AhmedHassanien34/Smart-Home/1- Code/Smart_Home_Master/MCAL/DIO/DIO_program.c

/**************************************************************************************/
/********************			Author: Ahmed Mohamed			***********************/
/********************			Layer: MCAL			 			***********************/
/********************			Component: DIO 				    ***********************/
/********************			Version: 2.00		 			***********************/
/********************			Date: 29-1-2023	 				***********************/
/**************************************************************************************/


#include "STD_TYPES.h"
#include "BIT_MATH.h"

#include "DIO_interface.h"
#include "DIO_register.h"
#include "DIO_private.h"
#include "DIO_config.h"


void DIO_voidInit(void)
{
	DIO_u8SetPinDirection(DIO_u8PORTA,DIO_u8PIN0,DIO_u8PIN_INPUT);
	DIO_u8SetPinDirection(DIO_u8PORTA,DIO_u8PIN1,DIO_u8PIN_INPUT);
	DIO_u8SetPinDirection(DIO_u8PORTA,DIO_u8PIN2,DIO_u8PIN_INPUT);
	DIO_u8SetPinDirection(DIO_u8PORTA,DIO_u8PIN3,DIO_u8PIN_INPUT);
	DIO_u8SetPinDirection(DIO_u8PORTA,DIO_u8PIN4,DIO_u8PIN_INPUT);
	DIO_u8SetPinDirection(DIO_u8PORTA,DIO_u8PIN5,DIO_u8PIN_INPUT);
	DIO_u8SetPinDirection(DIO_u8PORTA,DIO_u8PIN6,DIO_u8PIN_INPUT);

	DIO_u8SetPinDirection(DIO_u8PORTB,DIO_u8PIN0,DIO_u8PIN_OUTPUT);
	DIO_u8SetPinDirection(DIO_u8PORTB,DIO_u8PIN1,DIO_u8PIN_OUTPUT);

	DIO_u8SetPinDirection(DIO_u8PORTC,DIO_u8PIN0,DIO_u8PIN_OUTPUT);
	DIO_u8SetPinDirection(DIO_u8PORTC,DIO_u8PIN1,DIO_u8PIN_OUTPUT);
	DIO_u8SetPinDirection(DIO_u8PORTC,DIO_u8PIN2,DIO_u8PIN_OUTPUT);
	DIO_u8SetPinDirection(DIO_u8PORTC,DIO_u8PIN3,DIO_u8PIN_OUTPUT);
	DIO_u8SetPinDirection(DIO_u8PORTC,DIO_u8PIN4,DIO_u8PIN_OUTPUT);
	DIO_u8SetPinDirection(DIO_u8PORTC,DIO_u8PIN5,DIO_u8PIN_OUTPUT);
	DIO_u8SetPinDirection(DIO_u8PORTC,DIO_u8PIN6,DIO_u8PIN_OUTPUT);
	DIO_u8SetPinDirection(DIO_u8PORTC,DIO_u8PIN7,DIO_u8PIN_OUTPUT);

	DIO_u8SetPinDirection(DIO_u8PORTD,DIO_u8PIN6,DIO_u8PIN_OUTPUT);
}

u8 DIO_u8SetPinDirection(u8 Copy_u8Port, u8 Copy_u8Pin, u8 Copy_u8Direction)
{
	u8 Local_u8ErrorState=0;

	if(Copy_u8Pin <= DIO_u8PIN7)
	{
		if(Copy_u8Direction==DIO_u8PIN_INPUT)
		{
			switch(Copy_u8Port)
			{
			case DIO_u8PORTA: CLR_BIT(DDRA,Copy_u8Pin); break;
			case DIO_u8PORTB: CLR_BIT(DDRB,Copy_u8Pin); break;
			case DIO_u8PORTC: CLR_BIT(DDRC,Copy_u8Pin); break;
			case DIO_u8PORTD: CLR_BIT(DDRD,Copy_u8Pin); break;
			default: Local_u8ErrorState=1; break;
			}
		}
		else if (Copy_u8Direction==DIO_u8PIN_OUTPUT)
		{
			switch(Copy_u8Port)
			{
			case DIO_u8PORTA: SET_BIT(DDRA,Copy_u8Pin); break;
			case DIO_u8PORTB: SET_BIT(DDRB,Copy_u8Pin); break;
			case DIO_u8PORTC: SET_BIT(DDRC,Copy_u8Pin); break;
			case DIO_u8PORTD: SET_BIT(DDRD,Copy_u8Pin); break;
			default: Local_u8ErrorState=1; break;
			}
		}
		else if (Copy_u8Direction==DIO_u8PIN_INPULLUP)
		{
			switch(Copy_u8Port)
			{
			case DIO_u8PORTA: CLR_BIT(DDRA,Copy_u8Pin); SET_BIT(PORTA,Copy_u8Pin); break;
			case DIO_u8PORTB: CLR_BIT(DDRB,Copy_u8Pin); SET_BIT(PORTB,Copy_u8Pin); break;
			case DIO_u8PORTC: CLR_BIT(DDRC,Copy_u8Pin); SET_BIT(PORTC,Copy_u8Pin); break;
			case DIO_u8PORTD: CLR_BIT(DDRD,Copy_u8Pin); SET_BIT(PORTD,Copy_u8Pin); break;
			default: Local_u8ErrorState=1; break;
			}
		}
		else
		{
			Local_u8ErrorState=1;
		}
	}
	else
	{
		Local_u8ErrorState=1;
	}

	return Local_u8ErrorState;
}

u8 DIO_u8SetPortDirection(u8 Copy_u8Port, u8 Copy_u8Direction)
{
	u8 Local_u8ErrorState=0;

	switch(Copy_u8Port)
	{
	case DIO_u8PORTA : DDRA = Copy_u8Direction; break;
	case DIO_u8PORTB : DDRB = Copy_u8Direction; break;
	case DIO_u8PORTC : DDRC = Copy_u8Direction; break;
	case DIO_u8PORTD : DDRD = Copy_u8Direction; break;
	default: Local_u8ErrorState=1;
	}

	return Local_u8ErrorState;
}

u8 DIO_u8SetPinValue(u8 Copy_u8Port, u8 Copy_u8Pin, u8 Copy_u8Value)
{
	u8 Local_u8ErrorState=0;

	if(Copy_u8Pin<= DIO_u8PIN7)
	{
		if(Copy_u8Value==DIO_u8PIN_LOW)
		{
			switch(Copy_u8Port)
			{
			case DIO_u8PORTA: CLR_BIT(PORTA,Copy_u8Pin); break;
			case DIO_u8PORTB: CLR_BIT(PORTB,Copy_u8Pin); break;
			case DIO_u8PORTC: CLR_BIT(PORTC,Copy_u8Pin); break;
			case DIO_u8PORTD: CLR_BIT(PORTD,Copy_u8Pin); break;
			default: Local_u8ErrorState=1; break;
			}
		}
		else if (Copy_u8Value==DIO_u8PIN_HIGH)
		{
			switch(Copy_u8Port)
			{
			case DIO_u8PORTA: SET_BIT(PORTA,Copy_u8Pin); break;
			case DIO_u8PORTB: SET_BIT(PORTB,Copy_u8Pin); break;
			case DIO_u8PORTC: SET_BIT(PORTC,Copy_u8Pin); break;
			case DIO_u8PORTD: SET_BIT(PORTD,Copy_u8Pin); break;
			default: Local_u8ErrorState=1; break;
			}
		}
		else
		{
			Local_u8ErrorState=1;
		}
	}
	else
	{
		Local_u8ErrorState=1;
	}

	return Local_u8ErrorState;
}

u8 DIO_u8SetPortValue(u8 Copy_u8Port, u8 Copy_u8Value)
{
	u8 Local_u8ErrorState=0;

	switch(Copy_u8Port)
	{
	case DIO_u8PORTA : PORTA = Copy_u8Value; break;
	case DIO_u8PORTB : PORTB = Copy_u8Value; break;
	case DIO_u8PORTC : PORTC = Copy_u8Value; break;
	case DIO_u8PORTD : PORTD = Copy_u8Value; break;
	default: Local_u8ErrorState=1;
	}

	return Local_u8ErrorState;
}

u8 DIO_u8TogglePinValue(u8 Copy_u8Port, u8 Copy_u8Pin)
{
	u8 Local_u8ErrorState=0;

	switch (Copy_u8Port)
	{
	case DIO_u8PORTA: TOOGLE_BIT(PORTA,Copy_u8Pin); break;
	case DIO_u8PORTB: TOOGLE_BIT(PORTB,Copy_u8Pin); break;
	case DIO_u8PORTC: TOOGLE_BIT(PORTC,Copy_u8Pin); break;
	case DIO_u8PORTD: TOOGLE_BIT(PORTD,Copy_u8Pin); break;
	default: Local_u8ErrorState=1;
	}

	return Local_u8ErrorState;
}

u8 DIO_u8GetPinValue(u8 Copy_u8Port,u8 Copy_u8Pin, u8* Copy_pu8Value)
{
	u8 Local_u8ErrorState=0;

	if((Copy_pu8Value!=NULL) && (Copy_u8Pin<= DIO_u8PIN7))
	{
		switch(Copy_u8Port)
		{
		case DIO_u8PORTA : *Copy_pu8Value= GET_BIT(PINA , Copy_u8Pin); break;
		case DIO_u8PORTB : *Copy_pu8Value= GET_BIT(PINB , Copy_u8Pin); break;
		case DIO_u8PORTC : *Copy_pu8Value= GET_BIT(PINC , Copy_u8Pin); break;
		case DIO_u8PORTD : *Copy_pu8Value= GET_BIT(PIND , Copy_u8Pin); break;
		default: Local_u8ErrorState=1;
		}
	}
	else
	{
		Local_u8ErrorState=1;
	}
	return Local_u8ErrorState;
}

u8 DIO_u8GetPortValue(u8 Copy_u8Port , u8* Copy_pu8Value)
{
	u8 Local_u8ErrorState = 0;
	u8 Local_u8Counter;
	if(Copy_pu8Value != NULL)
	{
		switch(Copy_u8Port)
		{
		case DIO_u8PORTA: *Copy_pu8Value = PINA; break;
		case DIO_u8PORTB: *Copy_pu8Value = PINB; break;
		case DIO_u8PORTC: *Copy_pu8Value = PINC; break;
		case DIO_u8PORTD: *Copy_pu8Value = PIND; break;
		default: Local_u8ErrorState = 1; break;
		}
	}
	else
	{
		Local_u8ErrorState = 1;
	}
	return Local_u8ErrorState;
}
