AhmedHassanien34/Smart-Home/1- Code/Smart_Home_Slave/MCAL/DIO/DIO_register.h

/**************************************************************************************/
/********************			Author: Ahmed Mohamed			***********************/
/********************			Layer: MCAL			 			***********************/
/********************			Component: DIO 				    ***********************/
/********************			Version: 1.00		 			***********************/
/********************			Date: 16-12-2022	 			***********************/
/**************************************************************************************/


/* Preprocessor file guard */
#ifndef DIO_REGISTER_H_
#define DIO_REGISTER_H_

#define DDRA (*(volatile u8*)0x3A)
#define DDRB (*(volatile u8*)0x37)
#define DDRC (*(volatile u8*)0x34)
#define DDRD (*(volatile u8*)0x31)

#define PINA (*(volatile u8*)0x39)
#define PINB (*(volatile u8*)0x36)
#define PINC (*(volatile u8*)0x33)
#define PIND (*(volatile u8*)0x30)

#define PORTA (*(volatile u8*)0x3B)
#define PORTB (*(volatile u8*)0x38)
#define PORTC (*(volatile u8*)0x35)
#define PORTD (*(volatile u8*)0x32)

#endif
