AhmedHassanien34/Smart-Home/1- Code/Smart_Home_Master/MCAL/ADC/ADC_private.h

/**************************************************************************************/
/********************			Author: Ahmed Mohamed			***********************/
/********************			Layer: MCAL			 			***********************/
/********************			Component: ADC				    ***********************/
/********************			Version: 1.00		 			***********************/
/********************			Date: 16-12-2022	 			***********************/
/**************************************************************************************/


#ifndef ADC_PRIVATE_H_
#define ADC_PRIVATE_H_

#define AREF					            1
#define AVCC					            2
#define Internal_Voltage		            3

#define _8_Bits								1
#define _10_Bits							2

#define DivisionBy2 			            0
#define DivisionBy4 			            2
#define DivisionBy8  			            3
#define DivisionBy16 			            4
#define DivisionBy32 			            5
#define DivisionBy64 			            6
#define DivisionBy128			            7

#define IDLE								0
#define BUSY								1

#define SingleChannelAsynch					0
#define ChainAsynch							1


#endif
