AhmedHassanien34/Smart-Home/1- Code/Smart_Home_Master/MCAL/UART/UART_private.h

/*****************************************************************/
/***********		Author: Ahmed Mohamed 			**************/
/***********		Layer: MCAL			 			**************/
/***********		Component: UART			 		**************/
/***********		Version: 2.00		 			**************/
/***********		Date: 29-1-2023		 			**************/
/*****************************************************************/

#ifndef UART_PRIVATE_H_
#define UART_PRIVATE_H_

#define Enabled			                    1
#define Disabled		                    2

#define Asynchronous	                    1
#define Synchronous		                    2

#define Even			                    1
#define Odd				                    2

#define _1_bit			                    1
#define _2_bit			                    2

#define _5_bit			                    1
#define _6_bit			                    2
#define _7_bit			                    3
#define _8_bit			                    4
#define _9_bit			                    5

#define Rising_Edge		                    1
#define Falling_Edge	                    2

#define NormalSpeed		                    1
#define DoubleSpeed		                    2

#define IDLE		                        0
#define BUSY		                        1

#define SingleCharAsynch					0
#define ChainCharAsynch						1

#define ReceiveCharAsynch					0
#define ReceiveBufferAsynch					1
#endif
